RigacciOrg/ProTherm/case/images/openscad-protherm-complete.png

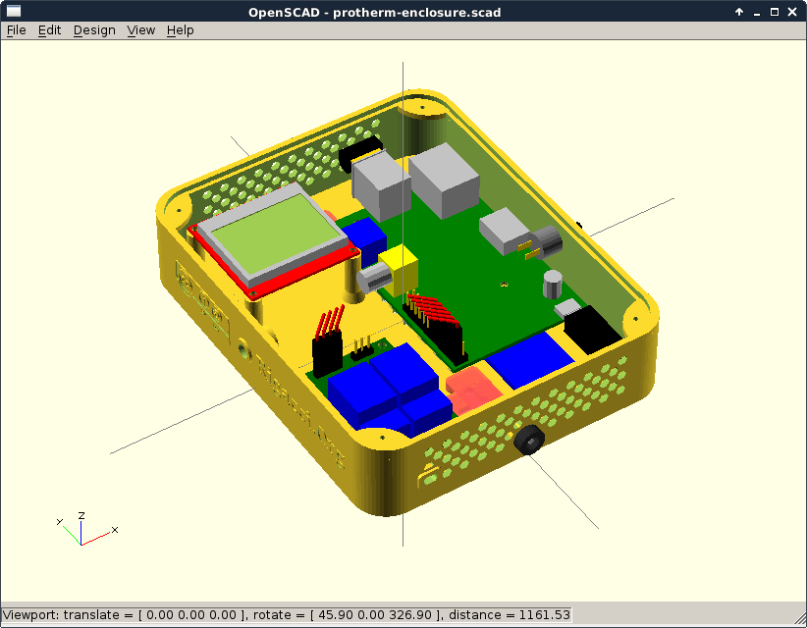
case/images/openscad-protherm-complete.png
