RigacciOrg/ProTherm/case/images/openscad-relay-lcd.png

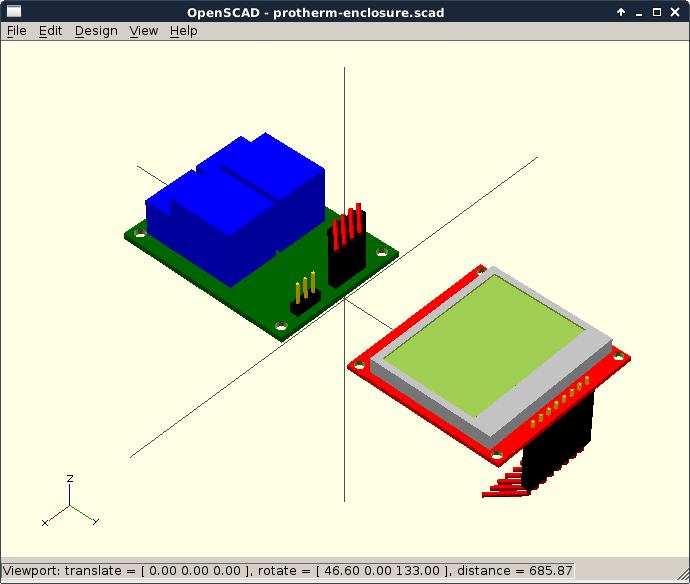
case/images/openscad-relay-lcd.png
