RigacciOrg/ProTherm/case/images/shapeways-photo.jpg

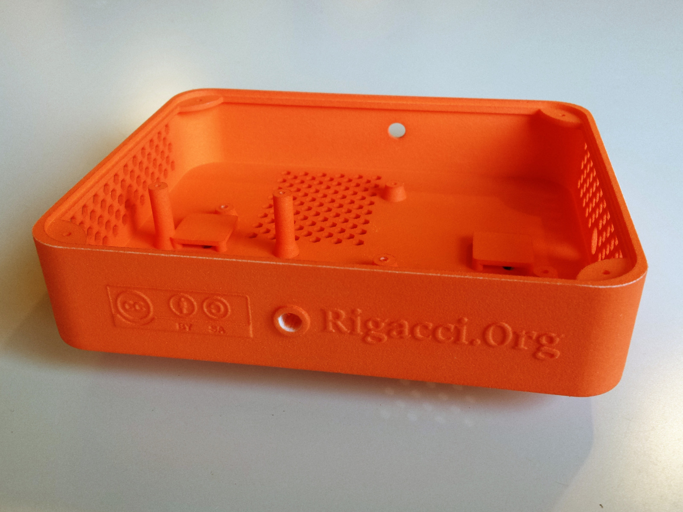
case/images/shapeways-photo.jpg
