RigacciOrg/ProTherm/case/scad/RigacciOrg.scad

// Module names are of the form poly_<inkscape-path-id>().  As a result,
// you can associate a polygon in this OpenSCAD program with the corresponding
// SVG element in the Inkscape document by looking for the XML element with
// the attribute id="inkscape-path-id".

// fudge value is used to ensure that subtracted solids are a tad taller
// in the z dimension than the polygon being subtracted from.  This helps
// keep the resulting .stl file manifold.
fudge = 0.1;

module poly_path3021(h)
{
  scale([25.4/90, -25.4/90, 1]) union()
  {
    difference()
    {
       linear_extrude(height=h)
         polygon([[-22.562615,6.002985],[-24.264395,7.068935],[-26.022275,7.966575],[-27.555745,8.602405],[-28.621695,8.845515],[-29.280914,8.653831],[-29.837255,8.078785],[-30.454385,5.946885],[-32.156165,7.349445],[-33.801845,8.247085],[-35.316615,8.714615],[-36.644375,8.845515],[-38.252655,8.565005],[-39.636515,7.723465],[-40.627665,6.339595],[-41.001685,4.432105],[-40.552865,2.356315],[-39.412105,0.785435],[-38.383555,-0.074805],[-36.793985,-0.897645],[-34.288065,-1.664375],[-30.473085,-2.393715],[-30.473085,-4.469515],[-30.585295,-5.498055],[-30.940605,-6.320895],[-31.613845,-6.844525],[-32.679795,-7.050235],[-33.483925,-6.881925],[-34.194565,-6.433105],[-34.680785,-5.685065],[-34.792995,-4.693925],[-35.129605,-4.394705],[-36.045945,-4.020685],[-37.261505,-3.646675],[-38.533165,-3.310055],[-39.599115,-3.104345],[-40.216245,-3.066945],[-40.665065,-4.170295],[-39.206395,-6.339595],[-36.868785,-8.078785],[-33.932745,-9.238235],[-30.641395,-9.668355],[-28.285085,-9.294335],[-26.658105,-8.303195],[-25.723065,-6.825825],[-25.423845,-5.030535],[-25.423845,3.459665],[-25.218135,4.581715],[-24.675815,4.918335],[-24.414005,4.899635],[-24.096085,4.824835],[-23.665965,4.675235],[-23.030135,4.413415],[-22.562615,6.002995]]);
       translate([0, 0, -fudge])
         linear_extrude(height=h+2*fudge)
           polygon([[-34.044955,5.292345],[-33.427825,5.236245],[-32.679795,4.993135],[-31.707345,4.432105],[-30.473085,3.478365],[-30.473085,-0.430125],[-32.156165,-0.112205],[-33.296915,0.205705],[-34.082355,0.542325],[-34.605985,0.953745],[-35.391415,1.963595],[-35.690635,3.253955],[-35.522325,4.245105],[-35.110905,4.880935],[-34.587285,5.198845],[-34.044955,5.292345]]);
    }
  }
}

module poly_path3025(h)
{
  scale([25.4/90, -25.4/90, 1]) union()
  {
    linear_extrude(height=h)
      polygon([[12.221025,4.731325],[9.939525,6.919325],[7.901125,8.153585],[6.031035,8.714615],[4.273155,8.845515],[2.735001,8.695910],[1.262315,8.247085],[-0.093506,7.499057],[-1.281005,6.489205],[-2.258131,5.222223],[-3.020195,3.702775],[-3.511091,1.949574],[-3.674725,-0.018705],[-3.487714,-1.972935],[-2.926685,-3.796275],[-2.029045,-5.437269],[-0.832185,-6.844525],[0.663878,-8.013318],[2.421765,-8.901625],[4.413406,-9.476656],[6.610765,-9.668355],[8.050735,-9.556155],[9.659005,-9.256935],[11.136375,-8.789415],[12.127525,-8.190985],[12.071425,-7.611255],[11.847015,-6.638815],[11.529095,-5.460655],[11.155075,-4.282505],[10.781065,-3.291355],[10.500545,-2.692925],[9.060575,-2.879935],[8.331245,-4.806125],[7.508405,-6.171295],[6.517255,-6.975425],[5.301705,-7.237245],[3.824335,-6.881925],[2.571375,-5.741175],[1.692435,-3.684075],[1.374515,-0.598425],[1.711135,2.000995],[2.683575,3.908485],[4.160945,5.086645],[5.993635,5.479355],[7.022185,5.423255],[8.106835,5.124045],[9.415895,4.488215],[11.117675,3.403565],[12.221025,4.731325]]);
  }
}

module poly_path3035(h)
{
  scale([25.4/90, -25.4/90, 1]) union()
  {
    difference()
    {
       linear_extrude(height=h)
         polygon([[94.467505,-3.702775],[94.308538,-2.323578],[93.831675,-1.065955],[92.129895,0.972445],[89.623975,2.300205],[86.594435,2.767735],[86.370025,2.767735],[85.565885,3.777575],[85.416285,4.245105],[85.491085,4.544315],[85.977305,4.824825],[87.174165,5.142745],[89.455675,5.479355],[93.177145,6.171295],[95.514755,7.106335],[96.730315,8.396695],[97.085635,10.154575],[96.674215,11.856355],[95.552155,13.520735],[93.869085,15.054215],[91.755885,16.288465],[89.399565,17.130005],[86.931055,17.447925],[84.817855,17.317015],[82.667255,16.942995],[80.666255,16.269765],[79.001875,15.297325],[77.861125,14.006965],[77.449705,12.379985],[77.655415,11.463645],[78.366045,10.453795],[79.768615,9.313035],[82.031425,7.929175],[80.460545,7.068935],[79.918225,6.171295],[80.778465,4.712625],[83.546195,2.375015],[81.582605,1.589575],[80.067825,0.411415],[79.095385,-1.122055],[78.758765,-2.973445],[78.931746,-4.301192],[79.450695,-5.554165],[81.302085,-7.686065],[83.995015,-9.126035],[87.267665,-9.668355],[89.792285,-9.294335],[91.905485,-8.303195],[93.382855,-8.583705],[94.766725,-8.957725],[95.963575,-9.331745],[96.879925,-9.668355],[97.440945,-8.920325],[97.272645,-8.434095],[97.010825,-7.835665],[96.692915,-7.199835],[96.374995,-6.676215],[95.122035,-6.489205],[93.719475,-6.377005],[94.280488,-5.091306],[94.467505,-3.702775]]);
       translate([0, 0, -fudge])
         linear_extrude(height=h+2*fudge)
           polygon([[89.605275,-2.936035],[89.380865,-4.675225],[88.726335,-6.096485],[87.641685,-7.068935],[86.164315,-7.424255],[85.247975,-7.218545],[84.425135,-6.582715],[83.845405,-5.535465],[83.620995,-4.039395],[83.808005,-2.281505],[84.425135,-0.878945],[85.509785,0.074805],[87.061955,0.430125],[88.071805,0.224415],[88.875945,-0.392715],[89.399565,-1.439965],[89.605275,-2.936035]]);
       translate([0, 0, -fudge])
         linear_extrude(height=h+2*fudge)
           polygon([[87.884795,9.294335],[84.537335,8.677205],[83.396585,9.649655],[82.798155,10.435095],[82.536345,11.089625],[82.498945,11.650655],[82.929065,12.754005],[84.125925,13.670345],[85.977305,14.306175],[88.333615,14.549285],[90.110205,14.287475],[91.325765,13.614245],[91.998995,12.660495],[92.223405,11.594545],[92.073795,10.958715],[91.456665,10.322885],[90.147605,9.743165],[87.884795,9.294335]]);
    }
  }
}

module poly_path3027(h)
{
  scale([25.4/90, -25.4/90, 1]) union()
  {
    linear_extrude(height=h)
      polygon([[13.978915,8.284495],[13.978915,6.732315],[15.830295,6.171295],[16.410025,5.591565],[16.410025,-3.684075],[16.391325,-5.217545],[16.185615,-6.133885],[15.474985,-6.620115],[13.978915,-6.863225],[13.978915,-8.359295],[17.214165,-8.882915],[20.075395,-9.668355],[21.459265,-9.668355],[21.459265,5.591565],[21.982885,6.152595],[23.890375,6.732315],[23.890375,8.284495],[13.978915,8.284495]]);
    linear_extrude(height=h)
      polygon([[22.207295,-15.297325],[21.945485,-14.081765],[21.216155,-13.146725],[20.112805,-12.566995],[18.747635,-12.361285],[17.662985,-12.473485],[16.746645,-12.866205],[16.092115,-13.558135],[15.848995,-14.530585],[16.110815,-15.746145],[16.858845,-16.662485],[17.943495,-17.242215],[19.308665,-17.447925],[20.374615,-17.317015],[21.290955,-16.942995],[21.945485,-16.269765],[22.207295,-15.297325]]);
  }
}

module poly_path3031(h)
{
  scale([25.4/90, -25.4/90, 1]) union()
  {
    difference()
    {
       linear_extrude(height=h)
         polygon([[58.374815,-3.814975],[57.944695,-0.523625],[56.766535,2.487215],[54.971255,5.067935],[52.633645,7.068935],[49.903315,8.377995],[46.911175,8.845515],[44.634333,8.597730],[42.591265,7.854375],[40.810006,6.694918],[39.318615,5.198845],[38.126429,3.408241],[37.242815,1.365165],[36.709840,-0.850881],[36.532185,-3.160445],[36.737895,-5.642982],[37.355025,-8.003975],[38.364869,-10.163916],[39.711335,-12.043365],[41.371033,-13.604875],[43.320605,-14.811095],[45.546000,-15.582492],[47.995825,-15.839645],[50.370825,-15.582492],[52.446635,-14.811095],[54.232558,-13.632927],[55.700585,-12.118175],[56.864701,-10.313522],[57.701585,-8.265795],[58.206493,-6.068427],[58.374815,-3.814975]]);
       translate([0, 0, -fudge])
         linear_extrude(height=h+2*fudge)
           polygon([[53.045065,-3.478365],[52.596245,-7.181135],[51.343285,-10.322885],[50.454978,-11.547777],[49.398385,-12.492185],[48.210875,-13.109300],[46.892475,-13.315025],[45.728334,-13.151380],[44.704465,-12.660495],[43.844221,-11.875045],[43.133595,-10.790405],[42.179845,-7.760865],[41.861935,-3.702775],[42.329455,0.205705],[43.601115,3.366155],[45.508605,5.460655],[46.630650,6.035710],[47.827515,6.227395],[48.907483,6.082464],[49.903315,5.647665],[50.805619,4.899631],[51.567695,3.852385],[52.652345,0.822835]]);
    }
  }
}

module poly_path3017(h)
{
  scale([25.4/90, -25.4/90, 1]) union()
  {
    linear_extrude(height=h)
      polygon([[-73.092395,8.284495],[-73.092395,6.732315],[-71.241005,6.171295],[-70.661285,5.591565],[-70.661285,-3.684075],[-70.679985,-5.217545],[-70.885695,-6.133885],[-71.596325,-6.620115],[-73.092395,-6.863225],[-73.092395,-8.359295],[-69.857145,-8.882915],[-66.995905,-9.668355],[-65.612045,-9.668355],[-65.612045,5.591565],[-65.088415,6.152595],[-63.180925,6.732315],[-63.180925,8.284495],[-73.092395,8.284495]]);
    linear_extrude(height=h)
      polygon([[-64.864005,-15.297325],[-65.125825,-14.081765],[-65.855155,-13.146725],[-66.958505,-12.566995],[-68.323675,-12.361285],[-69.408325,-12.473485],[-70.324665,-12.866205],[-70.979195,-13.558135],[-71.222305,-14.530585],[-70.960495,-15.746145],[-70.212465,-16.662485],[-69.127805,-17.242215],[-67.762645,-17.447925],[-66.696695,-17.317015],[-65.780355,-16.942995],[-65.125825,-16.269765],[-64.864005,-15.297325]]);
  }
}

module poly_path3029(h)
{
  scale([25.4/90, -25.4/90, 1]) union()
  {
    linear_extrude(height=h)
      polygon([[33.895355,5.797275],[33.596135,7.199835],[32.791995,8.209685],[31.613845,8.808115],[30.192575,9.032525],[29.089225,8.882915],[28.116775,8.415395],[27.443545,7.592555],[27.200435,6.377005],[27.499645,5.011835],[28.322485,3.983285],[29.519345,3.347455],[30.921915,3.123045],[31.969155,3.272655],[32.941605,3.758875],[33.633535,4.581715],[33.895355,5.797275]]);
  }
}

module poly_path3023(h)
{
  scale([25.4/90, -25.4/90, 1]) union()
  {
    linear_extrude(height=h)
      polygon([[-5.432605,4.731325],[-7.714115,6.919325],[-9.752505,8.153585],[-11.622595,8.714615],[-13.380475,8.845515],[-14.918634,8.695910],[-16.391325,8.247085],[-17.747139,7.499057],[-18.934645,6.489205],[-19.911766,5.222223],[-20.673825,3.702775],[-21.164721,1.949574],[-21.328355,-0.018705],[-21.141347,-1.972935],[-20.580315,-3.796275],[-19.682680,-5.437269],[-18.485825,-6.844525],[-16.989754,-8.013318],[-15.231865,-8.901625],[-13.240231,-9.476656],[-11.042865,-9.668355],[-9.602905,-9.556155],[-7.994625,-9.256935],[-6.517255,-8.789415],[-5.526105,-8.190985],[-5.582205,-7.611255],[-5.806615,-6.638815],[-6.124525,-5.460655],[-6.498545,-4.282505],[-6.872565,-3.291355],[-7.153075,-2.692925],[-8.593045,-2.879935],[-9.322375,-4.806125],[-10.145215,-6.171295],[-11.136365,-6.975425],[-12.351925,-7.237245],[-13.829295,-6.881925],[-15.082255,-5.741175],[-15.961195,-3.684075],[-16.279105,-0.598425],[-15.942495,2.000995],[-14.970045,3.908485],[-13.492675,5.086645],[-11.659985,5.479355],[-10.631445,5.423255],[-9.546785,5.124045],[-8.237725,4.488215],[-6.535945,3.403565],[-5.432595,4.731325]]);
  }
}

module poly_path3015(h)
{
  scale([25.4/90, -25.4/90, 1]) union()
  {
    difference()
    {
       linear_extrude(height=h)
         polygon([[-97.179135,8.284495],[-97.179135,6.732315],[-95.290345,6.171295],[-94.654515,5.591565],[-94.654515,-13.165425],[-97.179135,-12.810105],[-97.440945,-14.717595],[-92.915335,-15.484335],[-87.660385,-15.839645],[-83.153475,-15.409525],[-80.161335,-14.212675],[-79.165521,-13.375794],[-78.496955,-12.398685],[-77.973325,-10.173285],[-78.366045,-7.816965],[-79.431995,-5.872075],[-81.077675,-4.338605],[-83.190875,-3.272655],[-77.206595,4.563015],[-76.664265,5.198845],[-76.103235,5.572865],[-75.373905,5.703765],[-74.307955,5.666365],[-74.008735,7.218545],[-75.467405,7.667365],[-77.113085,8.097485],[-78.627855,8.415395],[-79.693805,8.546305],[-80.759755,8.247085],[-81.526495,7.517755],[-86.800145,-2.580725],[-87.118055,-2.562025],[-87.435975,-2.562025],[-88.408415,-2.599425],[-89.418265,-2.767735],[-89.418265,5.591565],[-88.838535,6.152595],[-86.893645,6.732315],[-86.893645,8.284495],[-97.179135,8.284495]]);
       translate([0, 0, -fudge])
         linear_extrude(height=h+2*fudge)
           polygon([[-88.539325,-13.707745],[-88.969445,-13.689045],[-89.418265,-13.689045],[-89.418265,-5.011835],[-88.539325,-4.899635],[-87.753885,-4.880935],[-85.715495,-5.198845],[-84.350325,-6.133885],[-83.564895,-7.611255],[-83.303075,-9.593555],[-83.527485,-11.145725],[-84.331625,-12.454785],[-85.939905,-13.371135]]);
    }
  }
}

module poly_path3033(h)
{
  scale([25.4/90, -25.4/90, 1]) union()
  {
    linear_extrude(height=h)
      polygon([[76.701675,-8.789415],[76.795175,-8.265795],[76.682975,-7.181135],[76.421155,-5.741175],[76.065845,-4.226395],[75.673125,-2.879935],[75.336505,-1.926195],[73.784335,-1.926195],[73.597325,-3.384855],[73.185905,-4.675225],[72.568775,-5.572865],[71.708535,-5.928175],[70.960505,-5.853375],[70.100265,-5.498055],[69.109115,-4.581715],[68.005765,-2.861235],[68.005765,5.591565],[68.791195,6.171295],[71.353225,6.732315],[71.353225,8.284495],[60.525405,8.284495],[60.525405,6.732315],[62.348743,6.166620],[62.956525,5.591565],[62.956525,-3.983285],[62.919125,-5.011835],[62.825625,-5.703765],[62.676025,-6.115185],[62.526415,-6.358305],[62.264605,-6.564005],[61.909285,-6.713615],[61.366955,-6.788415],[60.525415,-6.863215],[60.525415,-8.359285],[62.489015,-8.639795],[63.985085,-8.901615],[65.331545,-9.219525],[66.883715,-9.668345],[67.725255,-8.826805],[67.968375,-6.638805],[69.109125,-7.798255],[70.492985,-8.770705],[72.045165,-9.425235],[73.653435,-9.668345],[75.205615,-9.425235],[76.701685,-8.789405]]);
  }
}

module poly_path3019(h)
{
  scale([25.4/90, -25.4/90, 1]) union()
  {
    difference()
    {
       linear_extrude(height=h)
         polygon([[-45.115875,-3.702775],[-45.274846,-2.323578],[-45.751705,-1.065955],[-47.453485,0.972445],[-49.959405,2.300205],[-52.988945,2.767735],[-53.213355,2.767735],[-54.017495,3.777575],[-54.167105,4.245105],[-54.092305,4.544315],[-53.606075,4.824825],[-52.409225,5.142745],[-50.127715,5.479355],[-46.406235,6.171295],[-44.068625,7.106335],[-42.853075,8.396695],[-42.497755,10.154575],[-42.909175,11.856355],[-44.031225,13.520735],[-45.714305,15.054215],[-47.827505,16.288465],[-50.183815,17.130005],[-52.652335,17.447925],[-54.765535,17.317015],[-56.916135,16.942995],[-58.917125,16.269765],[-60.581505,15.297325],[-61.722265,14.006965],[-62.133685,12.379985],[-61.927975,11.463645],[-61.217335,10.453795],[-59.814775,9.313035],[-57.551965,7.929175],[-59.122835,7.068935],[-59.665165,6.171295],[-58.804925,4.712625],[-56.037195,2.375015],[-58.000785,1.589575],[-59.515555,0.411415],[-60.488005,-1.122055],[-60.824615,-2.973445],[-60.651638,-4.301192],[-60.132685,-5.554165],[-58.281295,-7.686065],[-55.588375,-9.126035],[-52.315715,-9.668355],[-49.791095,-9.294335],[-47.677895,-8.303195],[-46.200525,-8.583705],[-44.816665,-8.957725],[-43.619805,-9.331745],[-42.703465,-9.668355],[-42.142435,-8.920325],[-42.310745,-8.434095],[-42.572555,-7.835665],[-42.890475,-7.199835],[-43.208385,-6.676215],[-44.461345,-6.489205],[-45.863915,-6.377005],[-45.302898,-5.091306],[-45.115875,-3.702775]]);
       translate([0, 0, -fudge])
         linear_extrude(height=h+2*fudge)
           polygon([[-49.978105,-2.936035],[-50.202515,-4.675225],[-50.857045,-6.096485],[-51.941695,-7.068935],[-53.419065,-7.424255],[-54.335415,-7.218545],[-55.158255,-6.582715],[-55.737975,-5.535465],[-55.962385,-4.039395],[-55.775385,-2.281505],[-55.158255,-0.878945],[-54.073595,0.074805],[-52.521425,0.430125],[-51.511575,0.224415],[-50.707445,-0.392715],[-50.183815,-1.439965],[-49.978105,-2.936035]]);
       translate([0, 0, -fudge])
         linear_extrude(height=h+2*fudge)
           polygon([[-51.698585,9.294335],[-55.046045,8.677205],[-56.186795,9.649655],[-56.785225,10.435095],[-57.047045,11.089625],[-57.084445,11.650655],[-56.654325,12.754005],[-55.457465,13.670345],[-53.606075,14.306175],[-51.249765,14.549285],[-49.473185,14.287475],[-48.257625,13.614245],[-47.584395,12.660495],[-47.359985,11.594545],[-47.509595,10.958715],[-48.126715,10.322885],[-49.435785,9.743165],[-51.698585,9.294335]]);
    }
  }
}

module RigacciOrg(h)
{

poly_path3021(h);
poly_path3025(h);
poly_path3035(h);
poly_path3027(h);
poly_path3031(h);
poly_path3017(h);
poly_path3029(h);
poly_path3023(h);
poly_path3015(h);
poly_path3033(h);
poly_path3019(h);
}

//RigacciOrg(1);
